0xjmux/iot_leddriver_hw/files/PCB_v0.9.1_layout.png

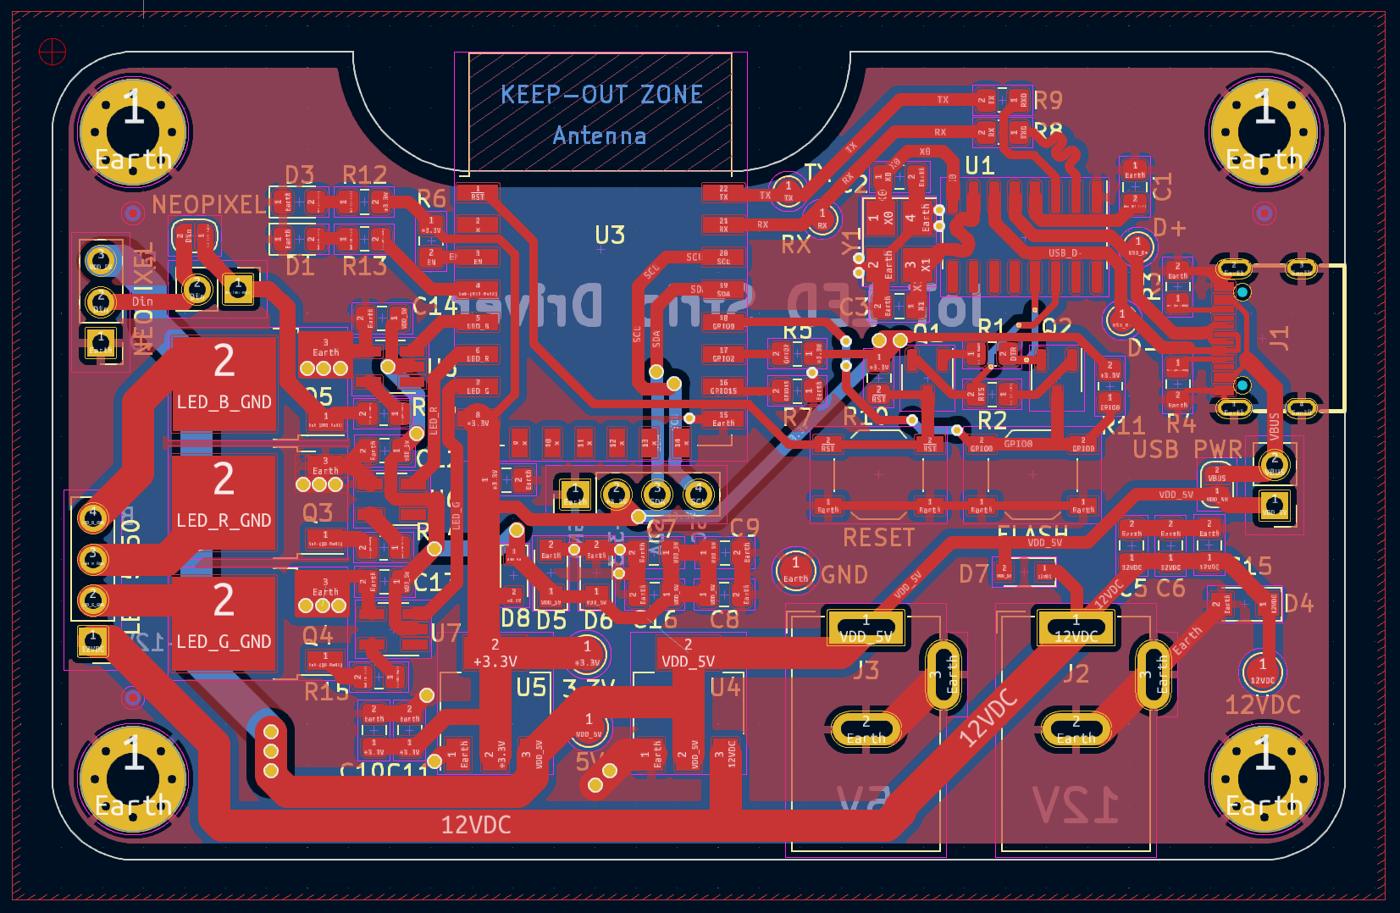
files/PCB_v0.9.1_layout.png
