0xjmux/iot_leddriver_hw/files/PCB_v1.0_render_F_RayT.png

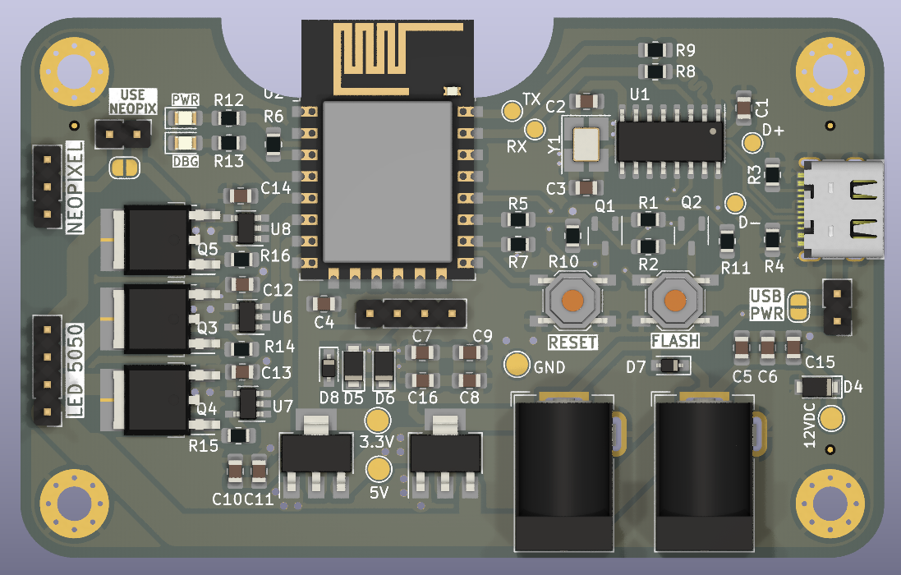
files/PCB_v1.0_render_F_RayT.png
